pramohan/me134/install/basic134/share/basic134/meshes/X8.stl

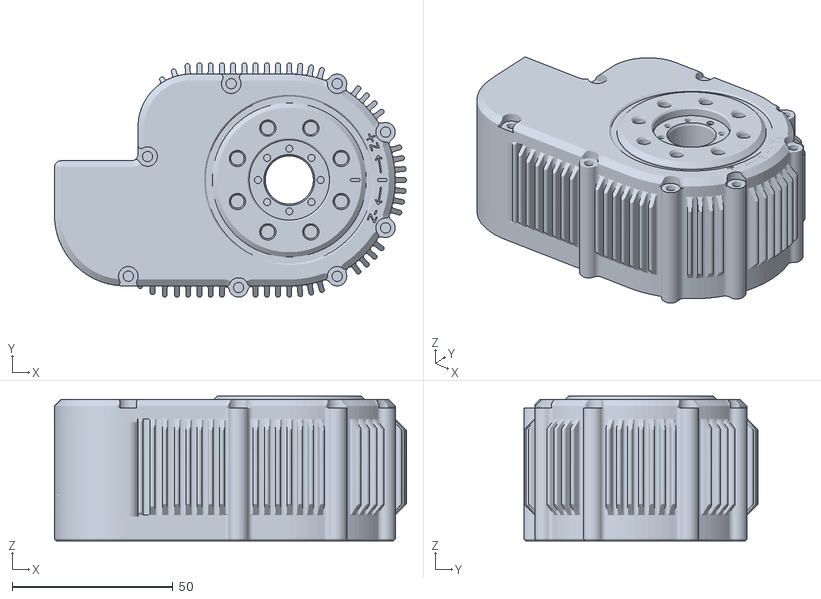
[picture p7: CAD file, 2023-02-03]
install/basic134/share/basic134/meshes/X8.stl
109.6 x 73.0 x 45.0
