pramohan/me134/install/basic134/share/basic134/meshes/lbracket.STL

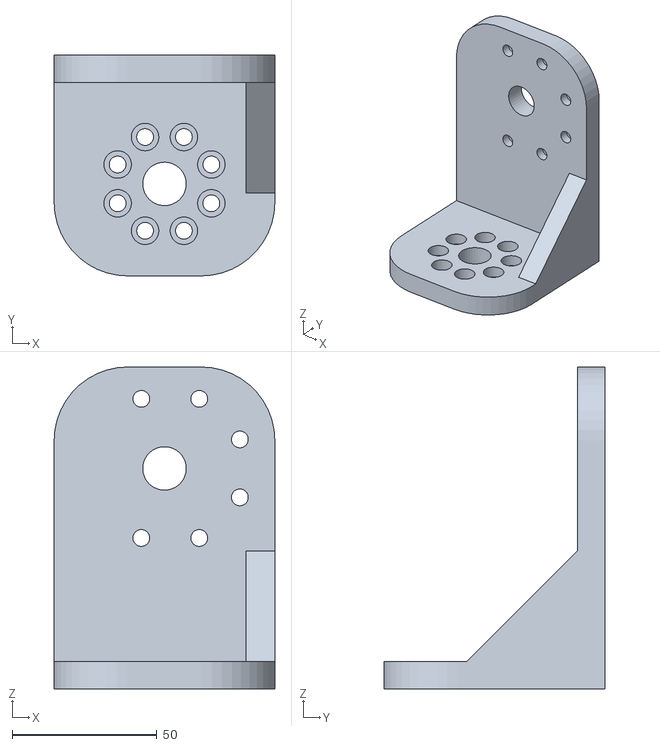
[picture p8: CAD file, 2023-02-03]
install/basic134/share/basic134/meshes/lbracket.STL
76.2 x 76.2 x 111.1
