pramohan/me134/install/operation/share/operation/meshes/arm_base.stl

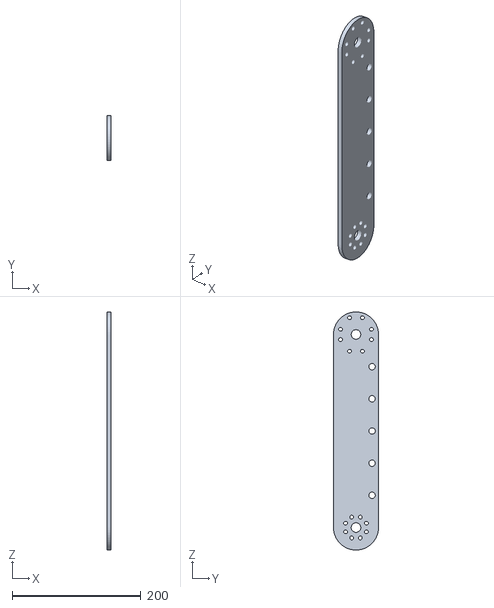
[picture p9: CAD file, 2023-02-03]
install/operation/share/operation/meshes/arm_base.stl
6.35 x 70.0 x 369.9
